arkadiuszmakarenko/CH32_DB9/firmware/User/gamepadAmiga.c

#include "gamepadAmiga.h"

void ProcessGamepadAmiga(HID_gamepad_Info_TypeDef* joymap)
{
			if (joymap == NULL) return;

			DUG_PRINTF( "Gamepad Amiga val(%02x)\r\n", joymap->gamepad_data );


               //RIGHT
               GPIO_WriteBit(PIN4_GPIO_Port, PIN4_Pin, !(joymap->gamepad_data & 0x1));

               //LEFT
               GPIO_WriteBit(PIN3_GPIO_Port, PIN3_Pin, !(joymap->gamepad_data >> 1 & 0x1));

               //DOWN
               GPIO_WriteBit(PIN2_GPIO_Port, PIN2_Pin, !(joymap->gamepad_data >> 2 & 0x1));

               //UP
               GPIO_WriteBit(PIN1_GPIO_Port, PIN1_Pin, !(joymap->gamepad_data >> 3 & 0x1));

               //BUTTON LEFT
               GPIO_WriteBit(PIN6_GPIO_Port, PIN6_Pin, !(joymap->gamepad_data >> 4 & 0x1));

               //BUTTON MIDDLE
               GPIO_WriteBit(PIN85_GPIO_Port, PIN85_Pin, !(joymap->gamepad_data >> 5 & 0x1));

               //BUTTON RIGHT
               GPIO_WriteBit(PIN79_GPIO_Port, PIN79_Pin, !(joymap->gamepad_data >> 6 & 0x1));

}
